Iqwertz/OpenPull-Web-Controller/OpenPull/CAD/Spacer.stl

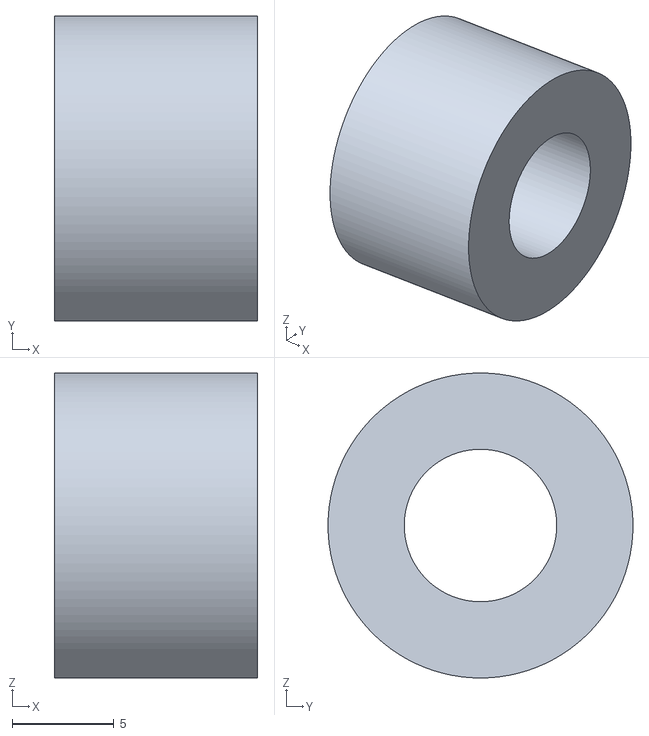
[picture p21: CAD file, 2021-02-02]
OpenPull/CAD/Spacer.stl
10.0 x 15.0 x 15.0
