Iqwertz/OpenPull-Web-Controller/OpenPull/CAD/PSU CASE.stl

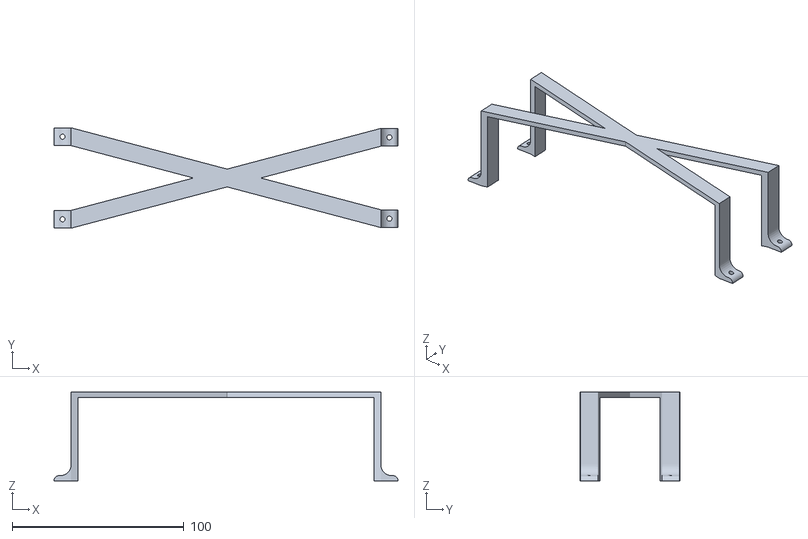
[picture p22: CAD file, 2021-02-02]
OpenPull/CAD/PSU CASE.stl
200.0 x 58.3 x 51.5
