Iqwertz/OpenPull-Web-Controller/OpenPull/CAD/UHakenSpacer.stl

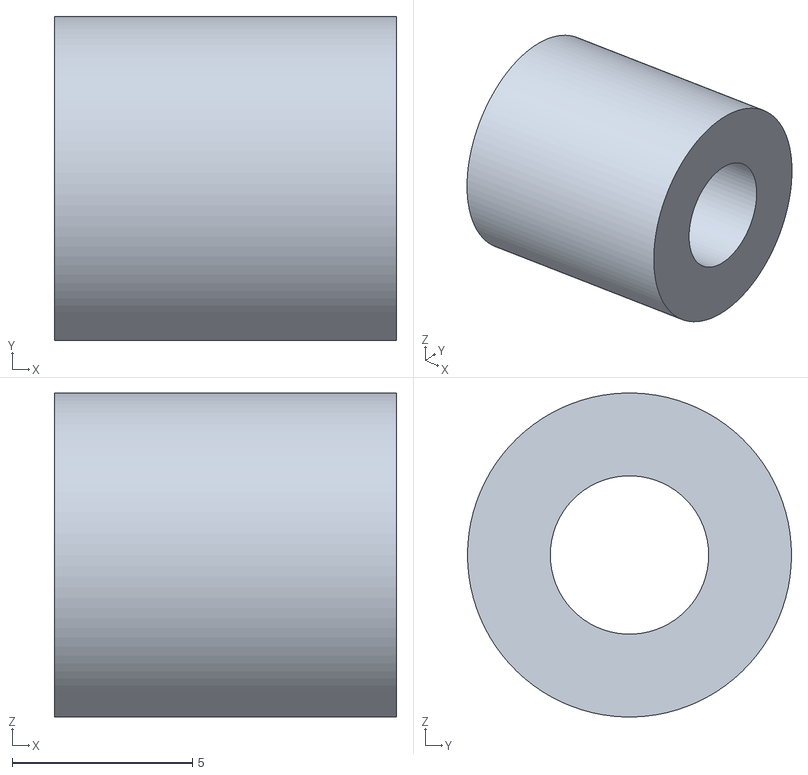
[picture p23: CAD file, 2021-02-02]
OpenPull/CAD/UHakenSpacer.stl
9.50 x 9.00 x 8.99
