Iqwertz/OpenPull-Web-Controller/OpenPull/CAD/BleSdCase.stl

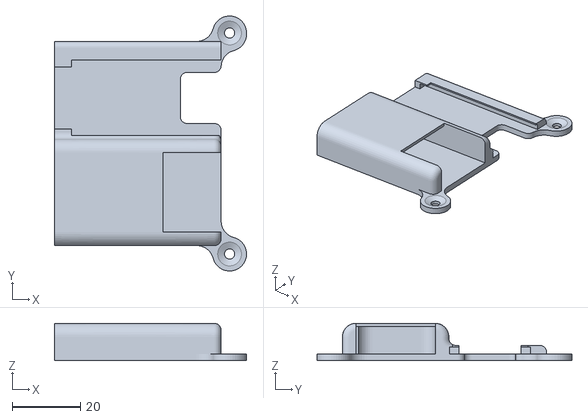
[picture p24: CAD file, 2021-02-02]
OpenPull/CAD/BleSdCase.stl
56.5 x 74.9 x 11.0
