Iqwertz/OpenPull-Web-Controller/OpenPull/CAD/UHaken.stl

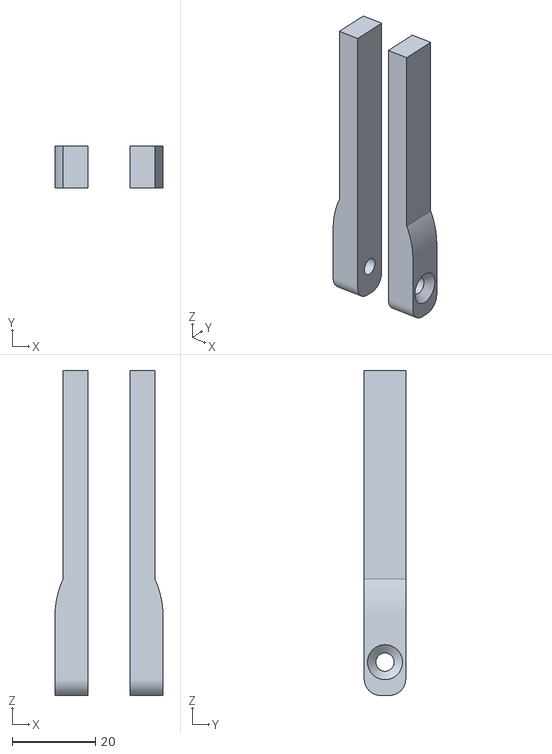
[picture p25: CAD file, 2021-02-02]
OpenPull/CAD/UHaken.stl
26.0 x 10.0 x 78.0
