Iqwertz/OpenPull-Web-Controller/OpenPull/CAD/Schräge2.stl

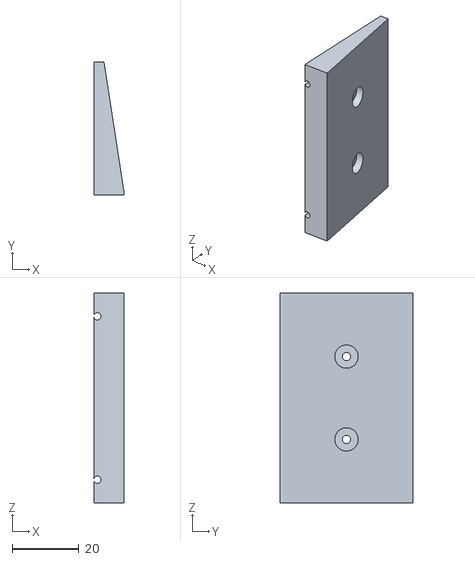
[picture p26: CAD file, 2021-02-02]
OpenPull/CAD/Schräge2.stl
9.00 x 40.0 x 63.0
