Iqwertz/OpenPull-Web-Controller/OpenPull/CAD/PSU Eck.stl

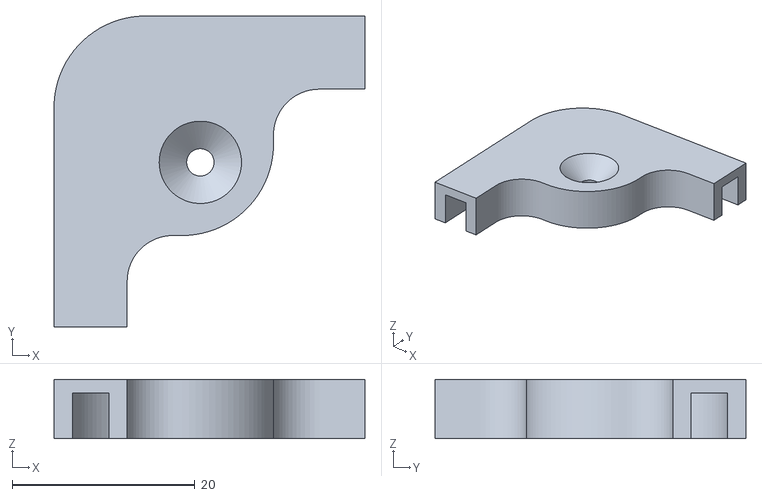
[picture p27: CAD file, 2021-02-02]
OpenPull/CAD/PSU Eck.stl
34.0 x 34.0 x 6.50
