Iqwertz/OpenPull-Web-Controller/OpenPull/CAD/Clampbreak.stl

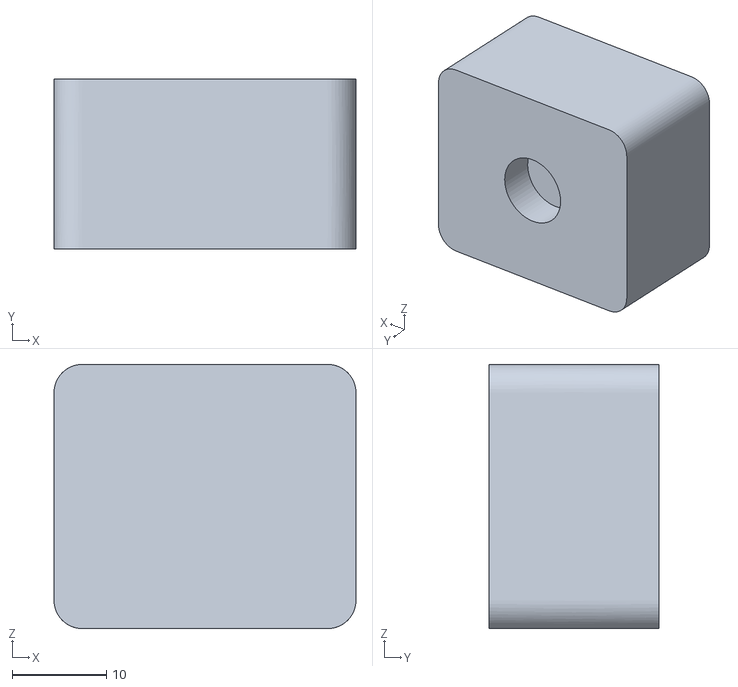
[picture p28: CAD file, 2021-02-02]
OpenPull/CAD/Clampbreak.stl
32.0 x 18.0 x 28.0
