Iqwertz/OpenPull-Web-Controller/OpenPull/CAD/Loadcell Kabel Eck.stl

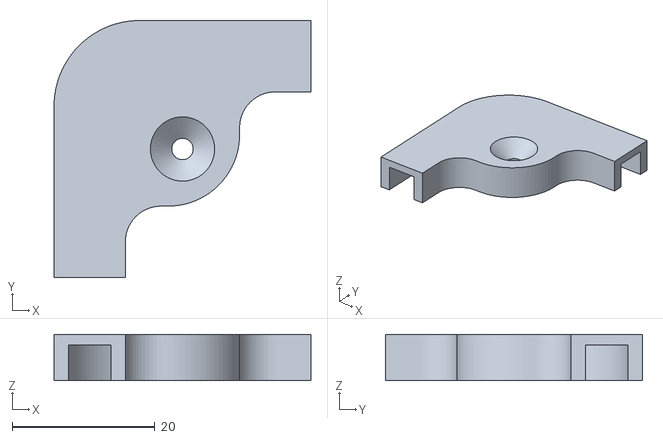
[picture p29: CAD file, 2021-02-02]
OpenPull/CAD/Loadcell Kabel Eck.stl
36.0 x 36.0 x 6.50
