Iqwertz/OpenPull-Web-Controller/OpenPull/CAD/Electroniccase.stl

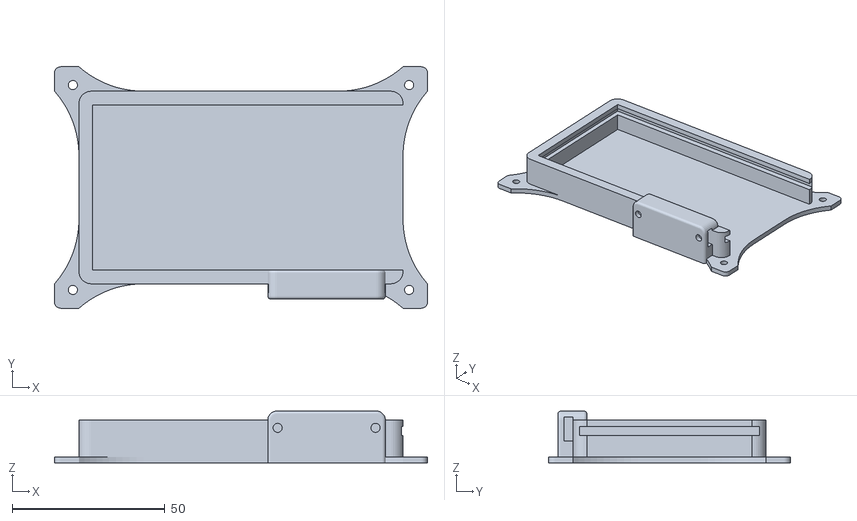
[picture p30: CAD file, 2021-02-02]
OpenPull/CAD/Electroniccase.stl
122.0 x 79.0 x 17.0
