Iqwertz/OpenPull-Web-Controller/OpenPull/CAD/Dreher.stl

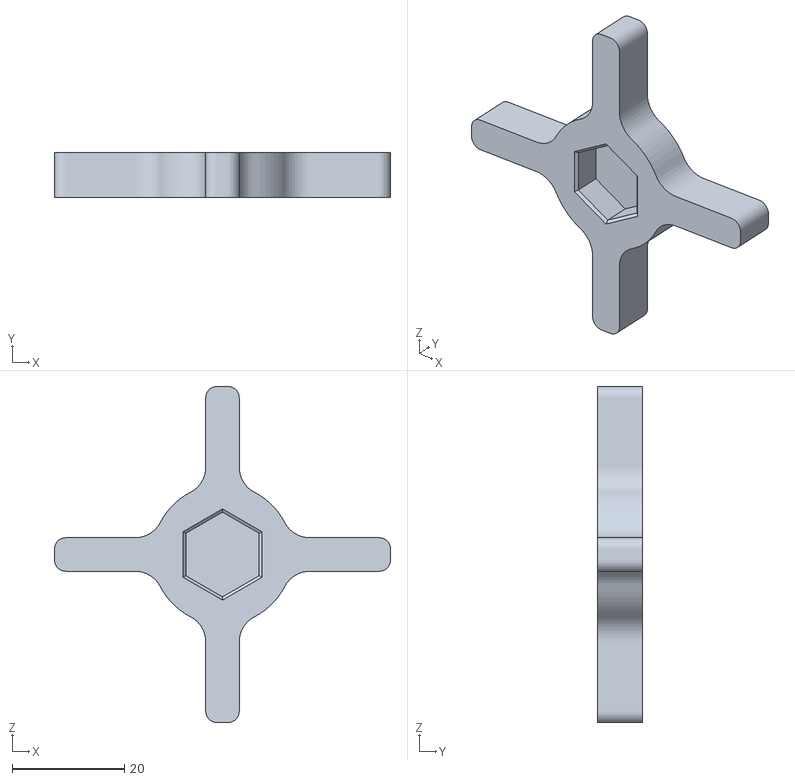
[picture p31: CAD file, 2021-02-02]
OpenPull/CAD/Dreher.stl
60.0 x 8.00 x 60.0
