Iqwertz/OpenPull-Web-Controller/OpenPull/CAD/Leitung2.stl

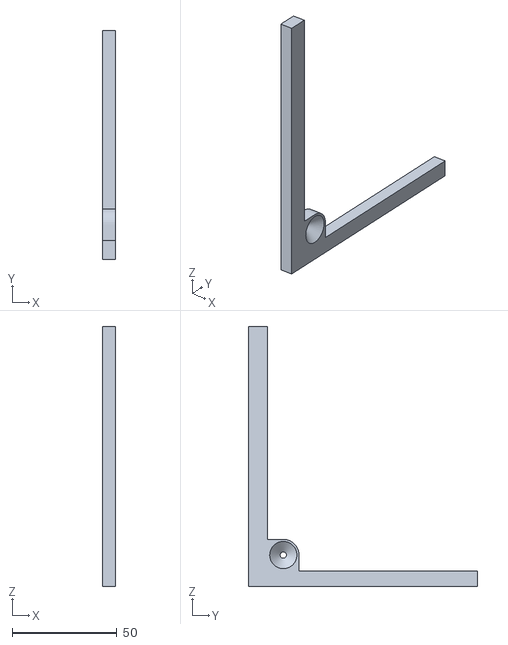
[picture p32: CAD file, 2021-02-02]
OpenPull/CAD/Leitung2.stl
6.00 x 109.0 x 124.0
