Iqwertz/OpenPull-Web-Controller/OpenPull/CAD/PSU CASE Half.stl

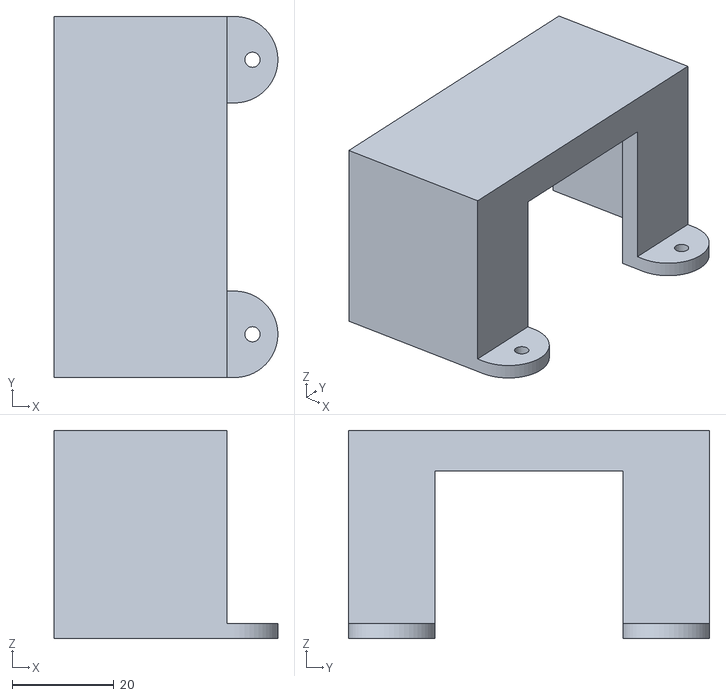
[picture p33: CAD file, 2021-02-02]
OpenPull/CAD/PSU CASE Half.stl
44.0 x 71.0 x 41.0
