Iqwertz/OpenPull-Web-Controller/OpenPull/CAD/Loadcell Kabel Klemme.stl

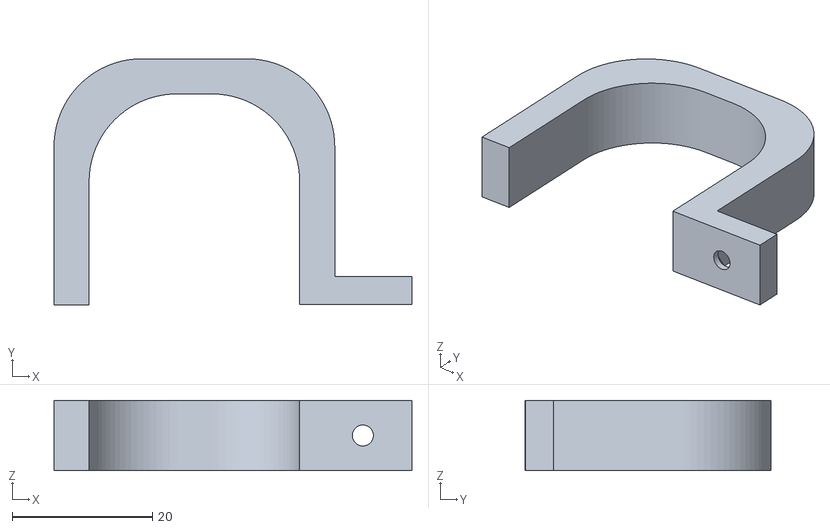
[picture p34: CAD file, 2021-02-02]
OpenPull/CAD/Loadcell Kabel Klemme.stl
51.0 x 35.1 x 10.0
