Iqwertz/OpenPull-Web-Controller/OpenPull/CAD/NutHolder.stl

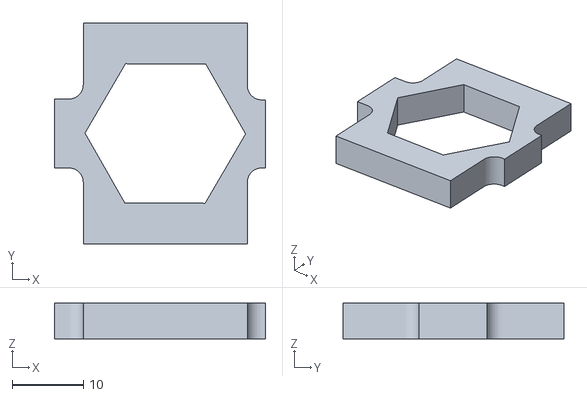
[picture p35: CAD file, 2021-02-02]
OpenPull/CAD/NutHolder.stl
29.6 x 31.0 x 5.00
