Iqwertz/OpenPull-Web-Controller/OpenPull/CAD/DriverBottomSpacer.stl

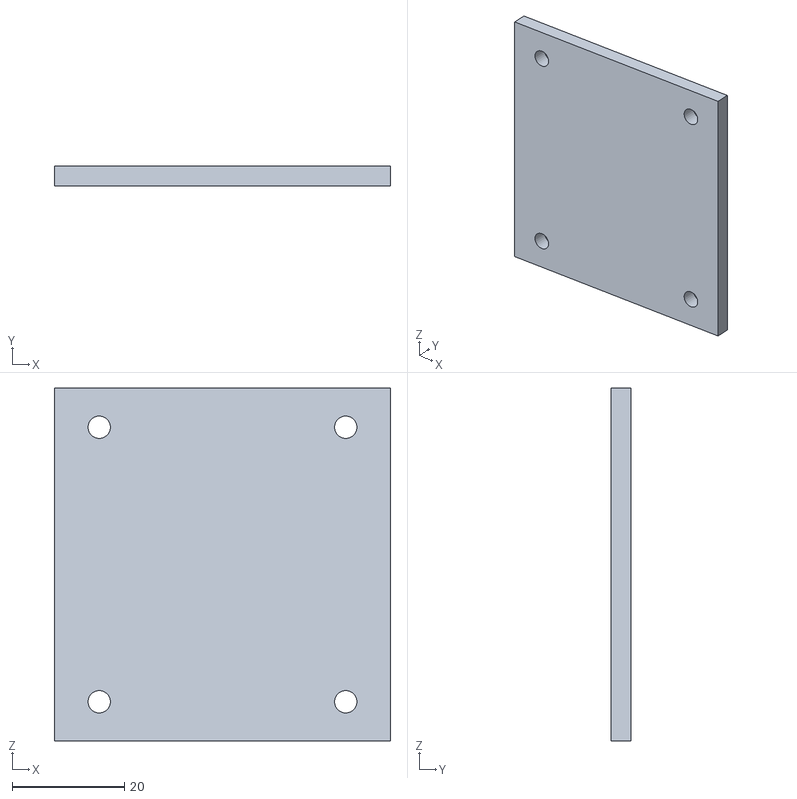
[picture p36: CAD file, 2021-02-02]
OpenPull/CAD/DriverBottomSpacer.stl
60.0 x 3.50 x 63.0
